znhocn/xiaomi2ali-smart-plug-wifi-module/Images/IMG_0003.jpg

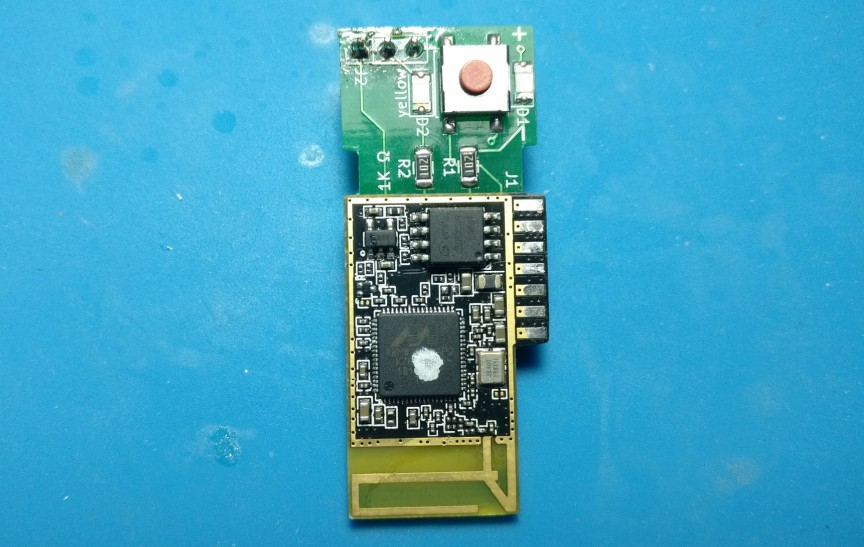
Images/IMG_0003.jpg
