znhocn/xiaomi2ali-smart-plug-wifi-module/Images/IMG_0004.jpg

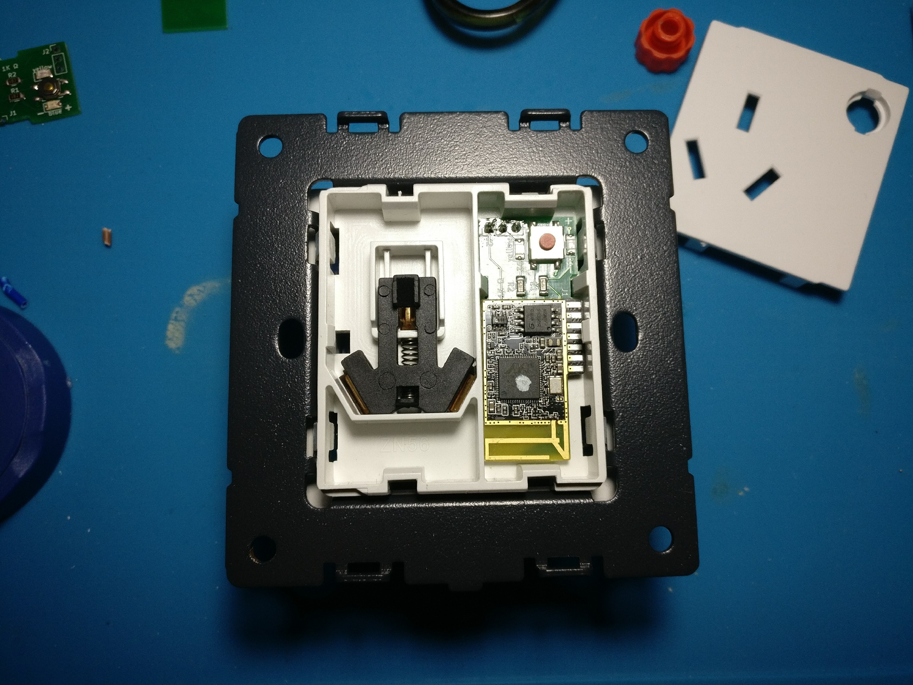
Images/IMG_0004.jpg
